JosephMelesse/electric_beats/web/client/src/assets/team_pics/dante.jpg

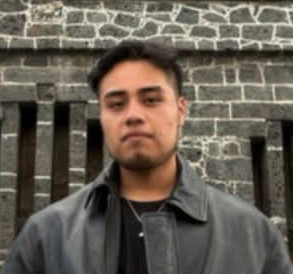
web/client/src/assets/team_pics/dante.jpg
