JosephMelesse/electric_beats/web/client/src/assets/team_pics/khai.jpg

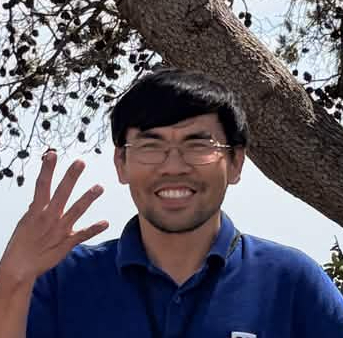
web/client/src/assets/team_pics/khai.jpg
